AJMartel/BoomBox/fusecontrol.jpg

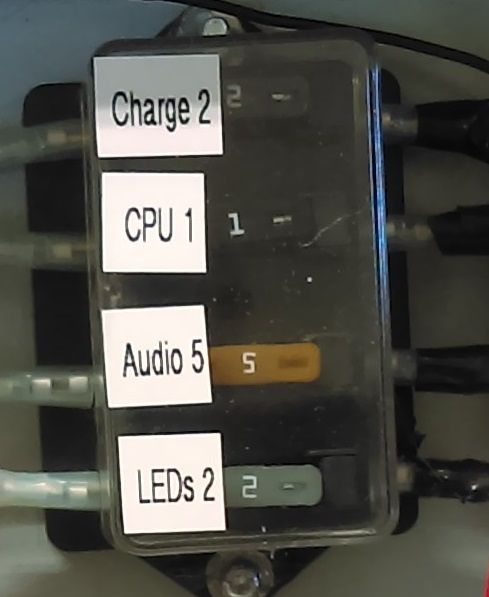
fusecontrol.jpg
