AJMartel/BoomBox/FusePower.jpg

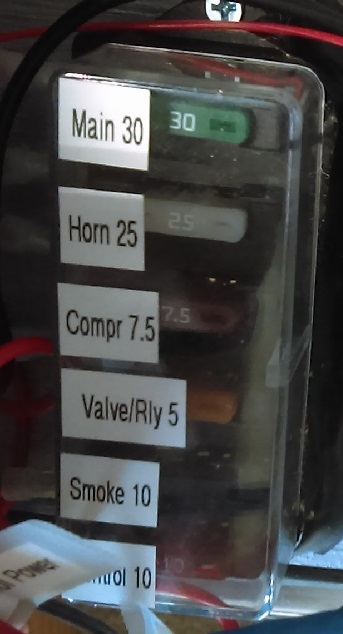
FusePower.jpg
