AJMartel/BoomBox/IMAG0399.jpg

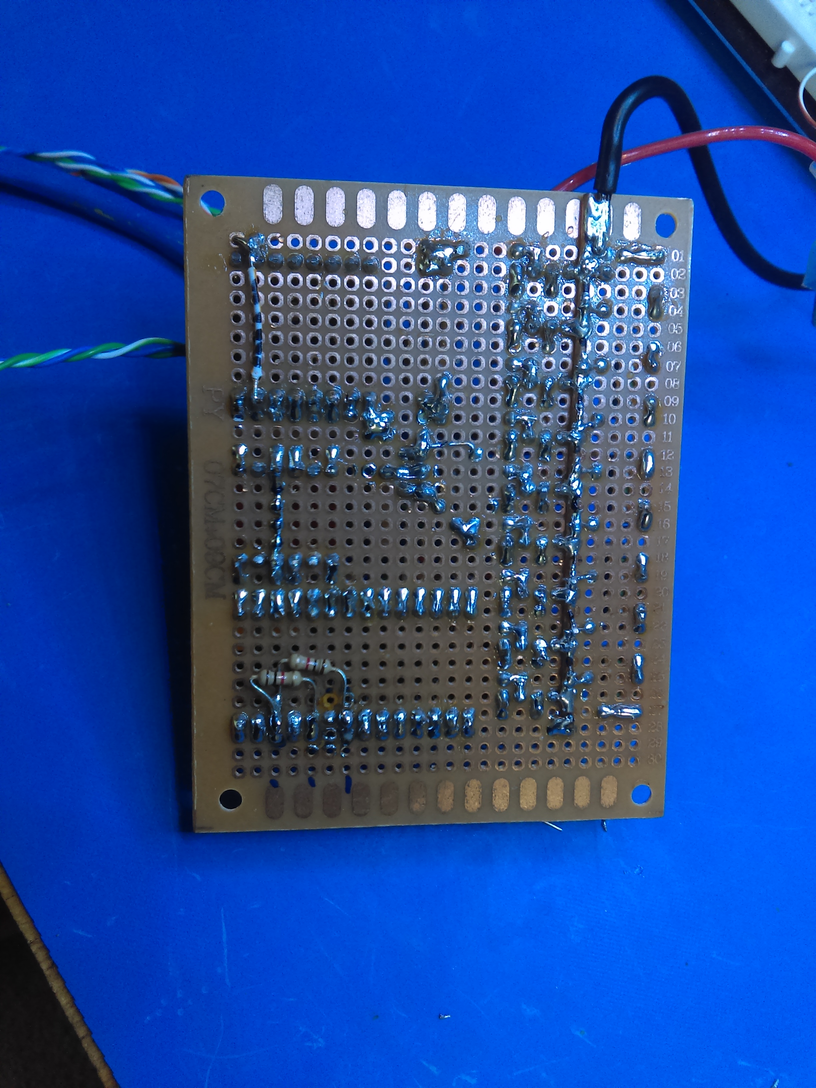
IMAG0399.jpg
