AJMartel/BoomBox/IMAG0400.jpg

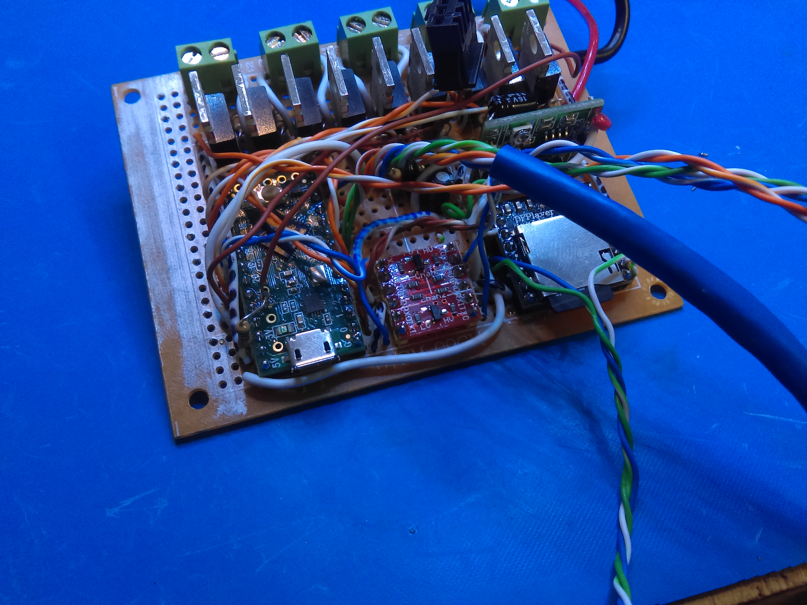
IMAG0400.jpg
