AJMartel/BoomBox/IMAG0402.jpg

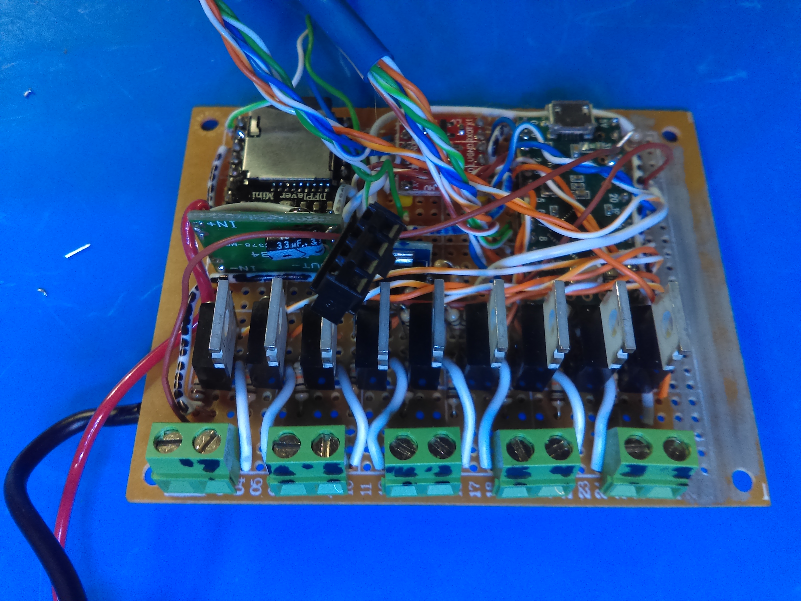
IMAG0402.jpg
