AJMartel/BoomBox/IMAG0403.jpg

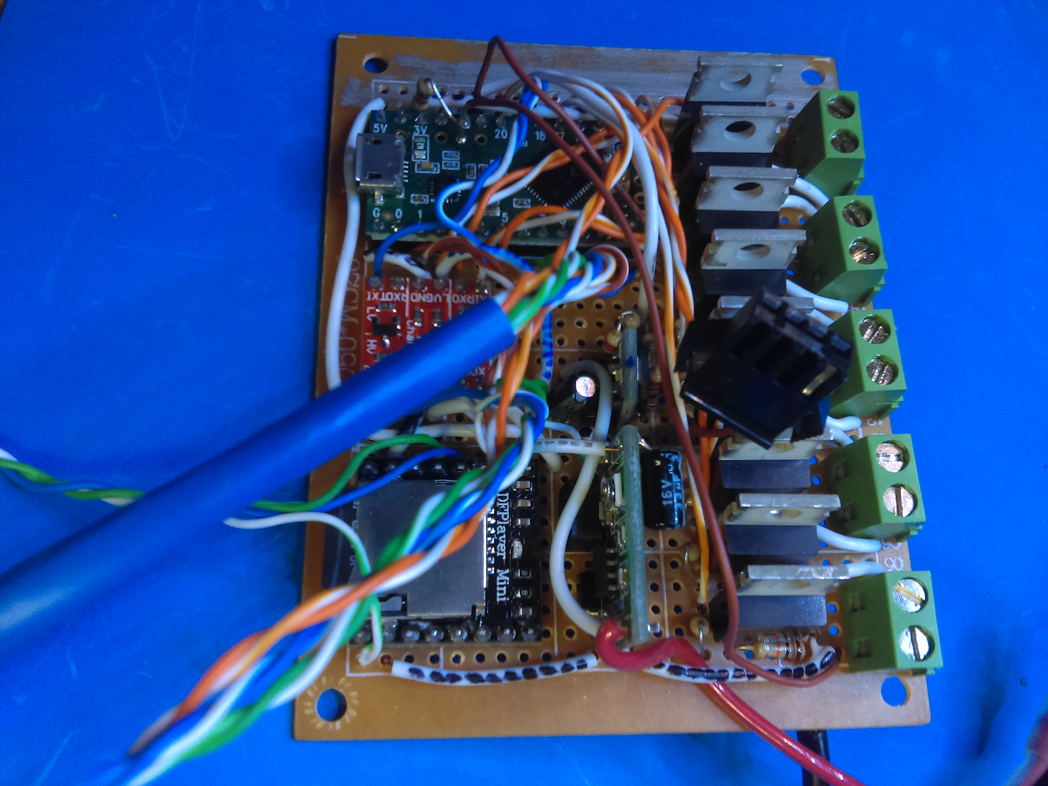
IMAG0403.jpg
