AJMartel/BoomBox/IMAG0406.jpg

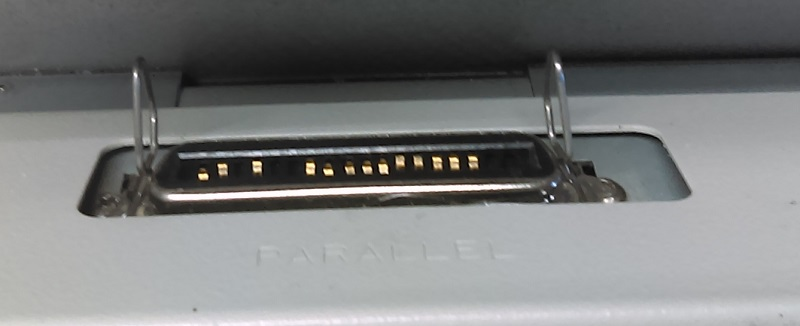
IMAG0406.jpg
