AJMartel/BoomBox/IMAG0410.jpg

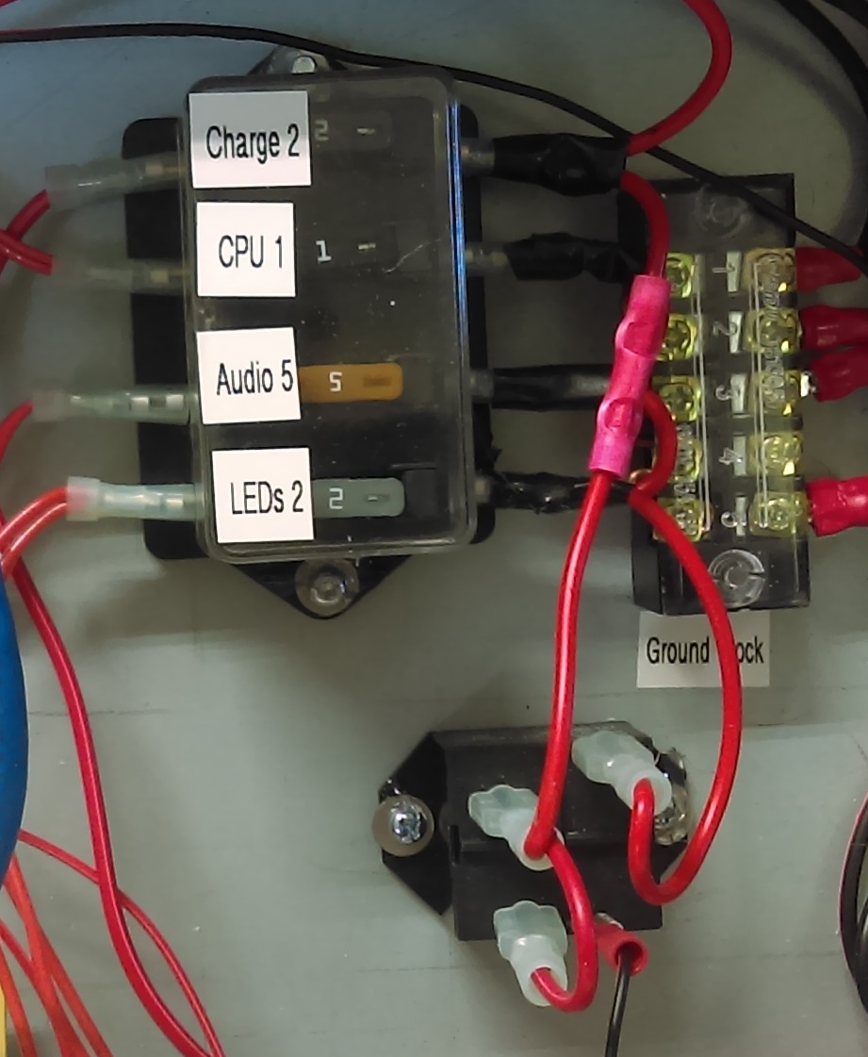
IMAG0410.jpg
