AJMartel/BoomBox/IMAG0411.jpg

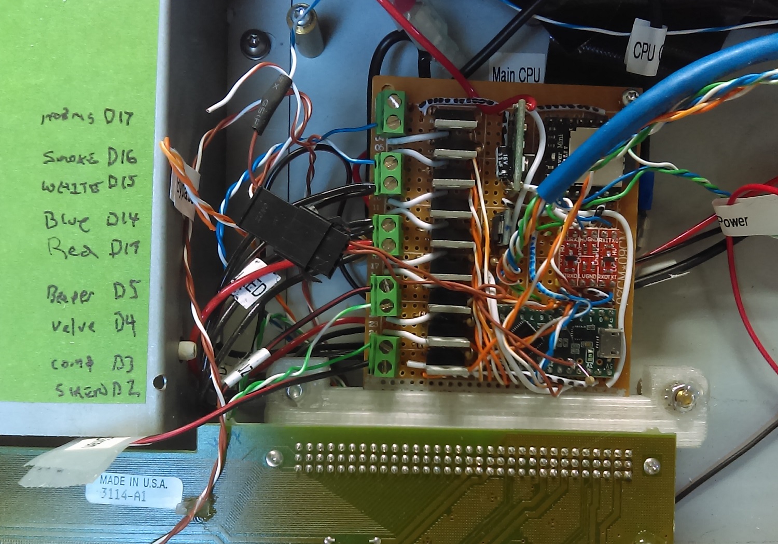
IMAG0411.jpg
