AJMartel/BoomBox/IMAG0413.jpg

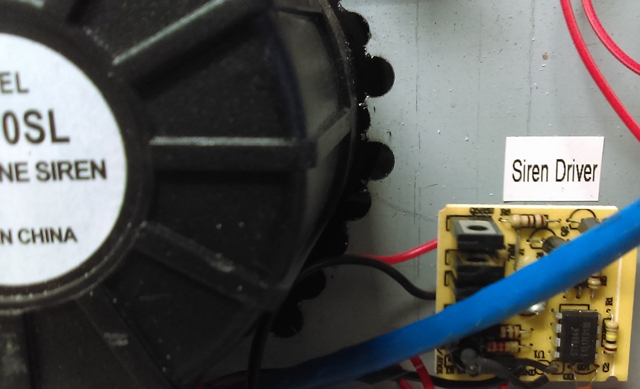
IMAG0413.jpg
