AJMartel/BoomBox/IMAG0414.jpg

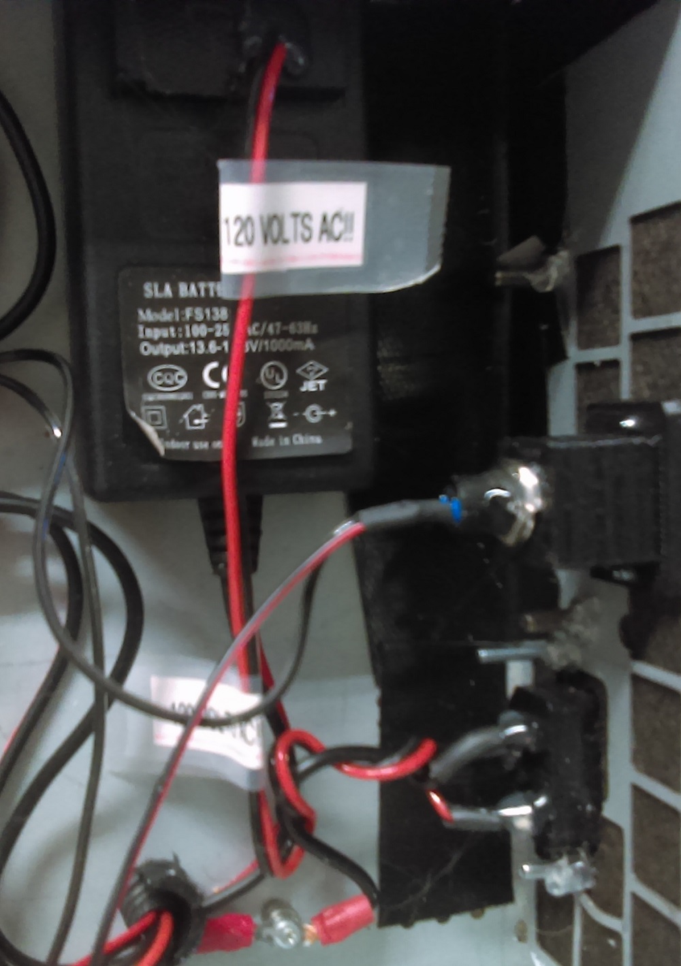
IMAG0414.jpg
