AJMartel/BoomBox/IMAG0417.jpg

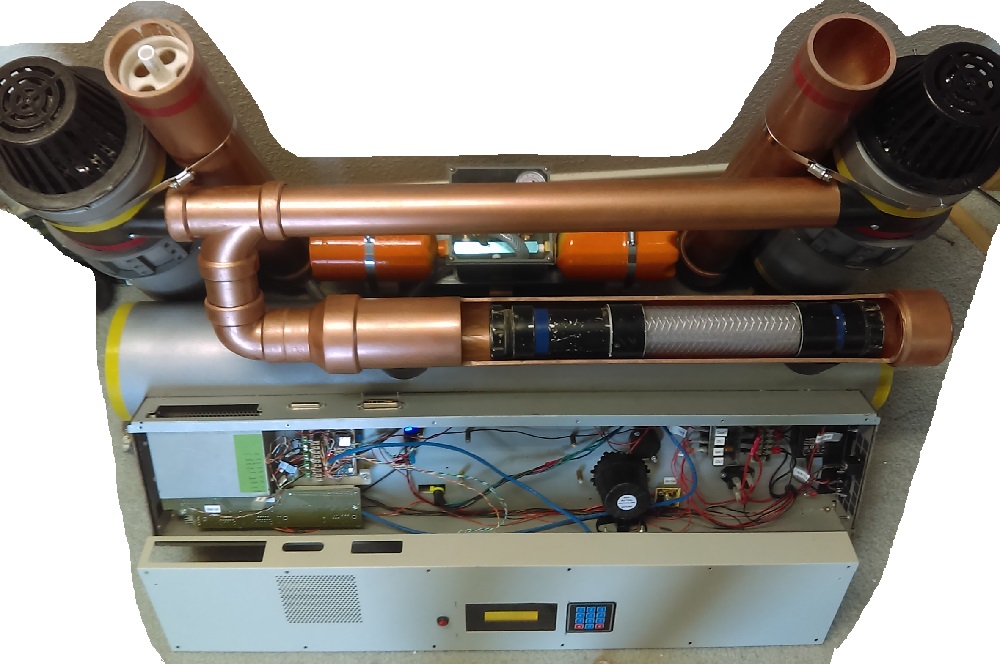
IMAG0417.jpg
