AJMartel/BoomBox/IMAG0419.jpg

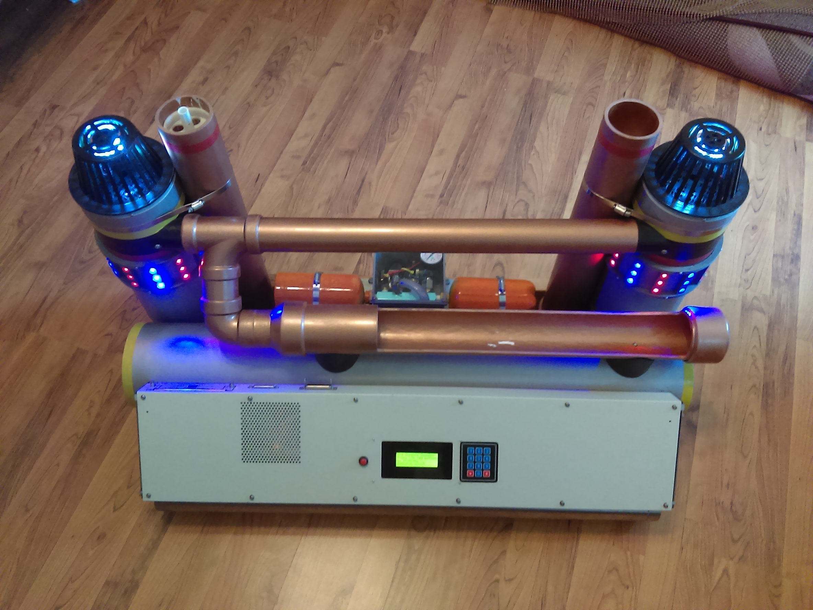
IMAG0419.jpg
