AJMartel/BoomBox/IMAG0420.jpg

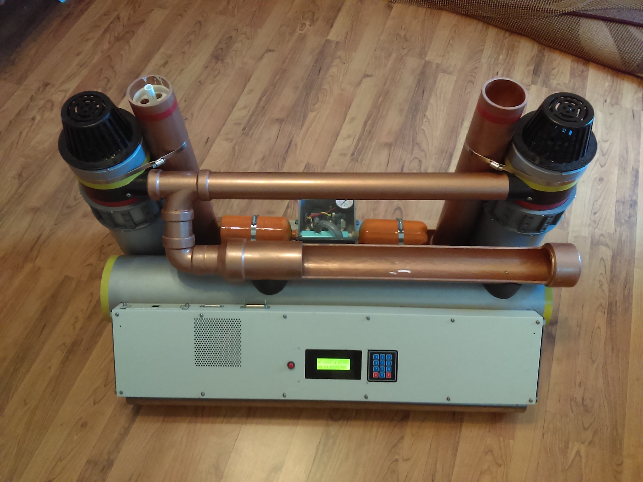
IMAG0420.jpg
