AJMartel/BoomBox/IMAG0421.jpg

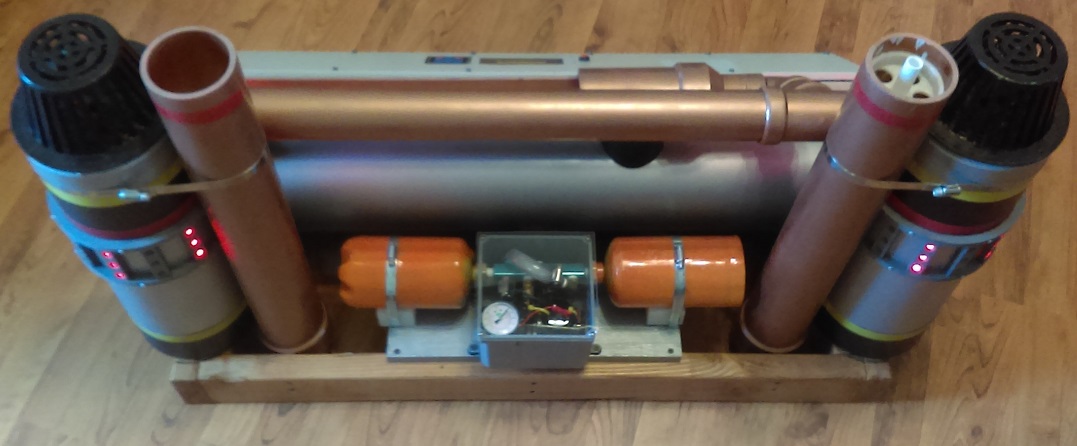
IMAG0421.jpg
