AJMartel/BoomBox/IMAG0423.jpg

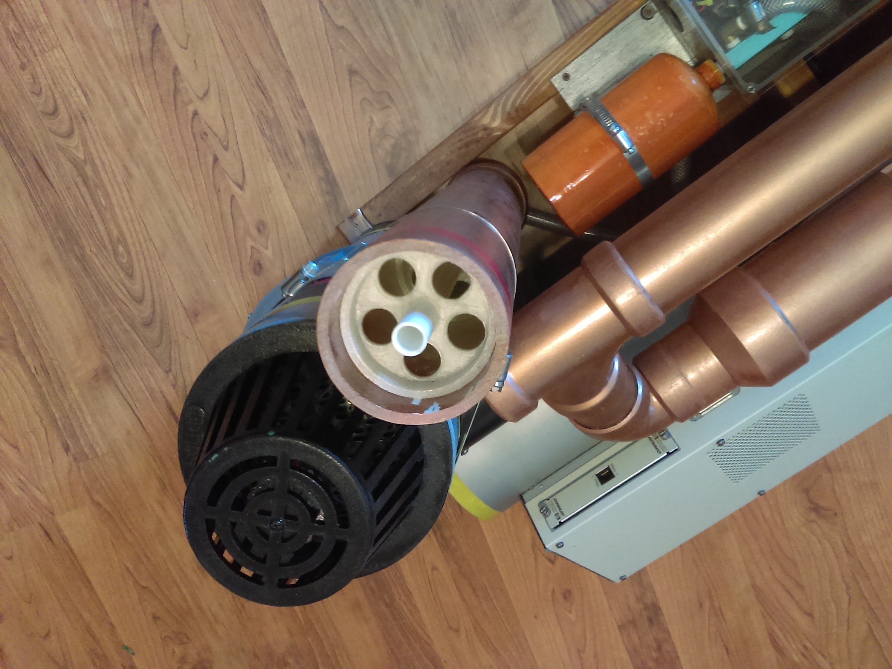
IMAG0423.jpg
