AJMartel/BoomBox/IMAG0424.jpg

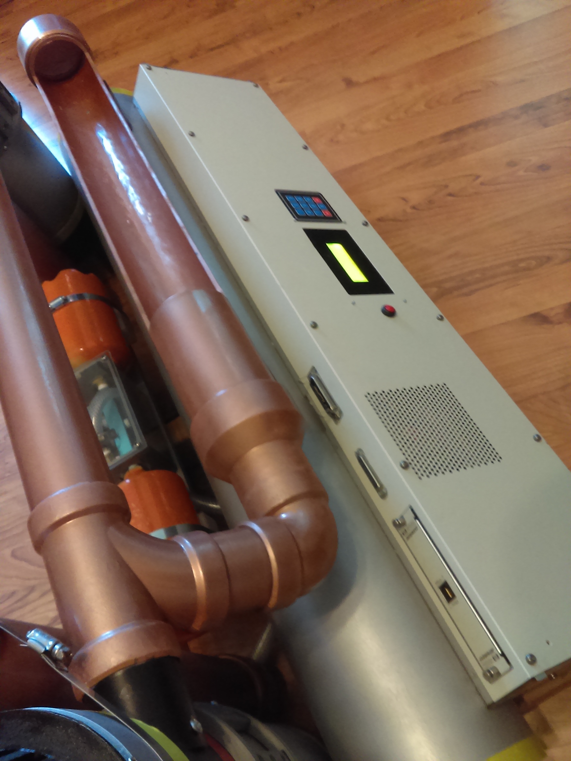
IMAG0424.jpg
