AJMartel/BoomBox/IMAG0426.jpg

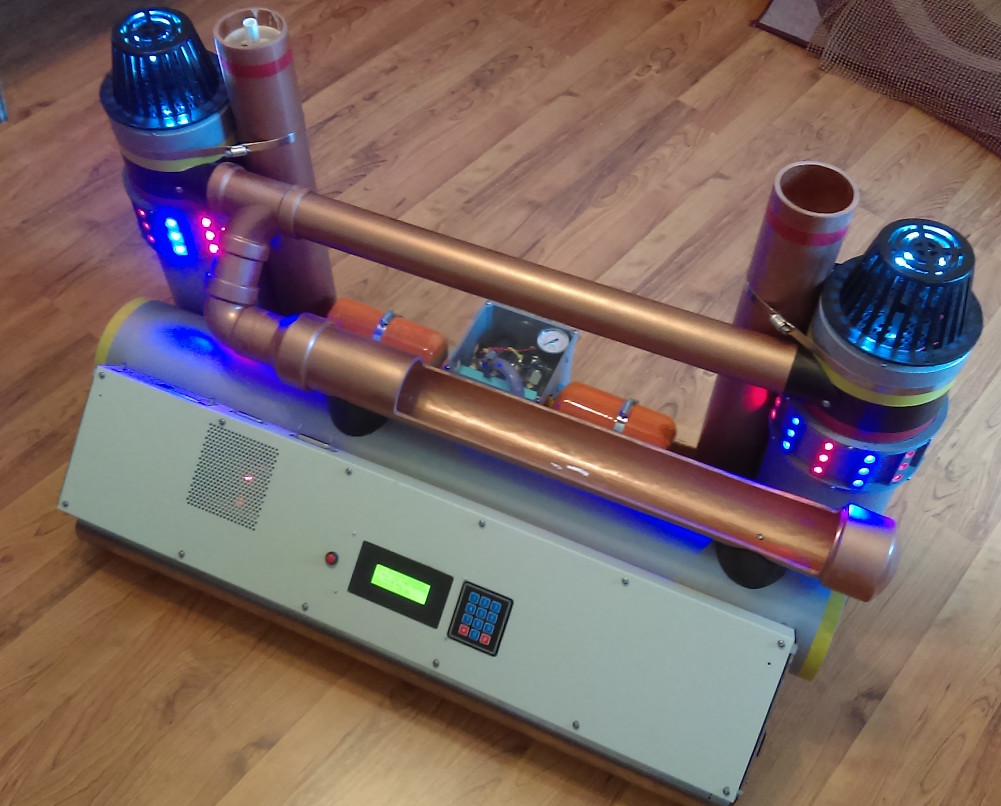
IMAG0426.jpg
