AJMartel/BoomBox/IMAG0428.jpg

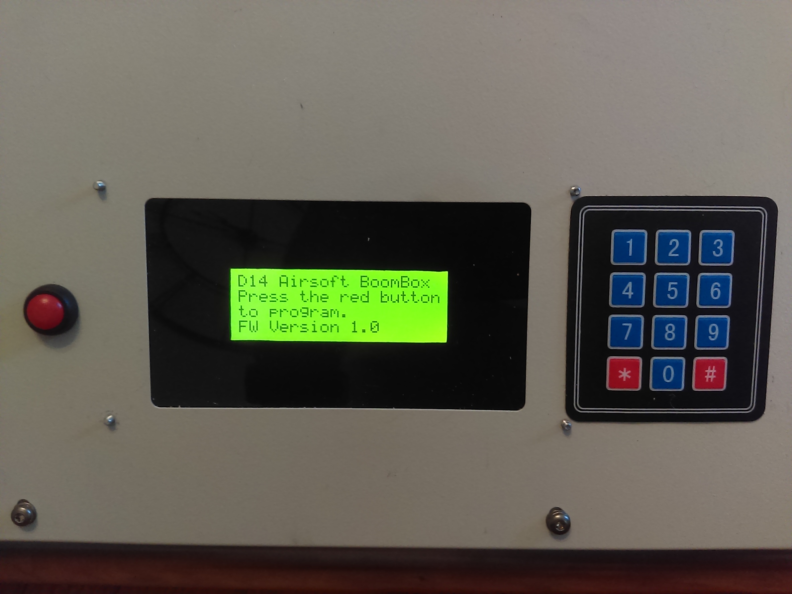
IMAG0428.jpg
