AJMartel/BoomBox/IMAG0429.jpg

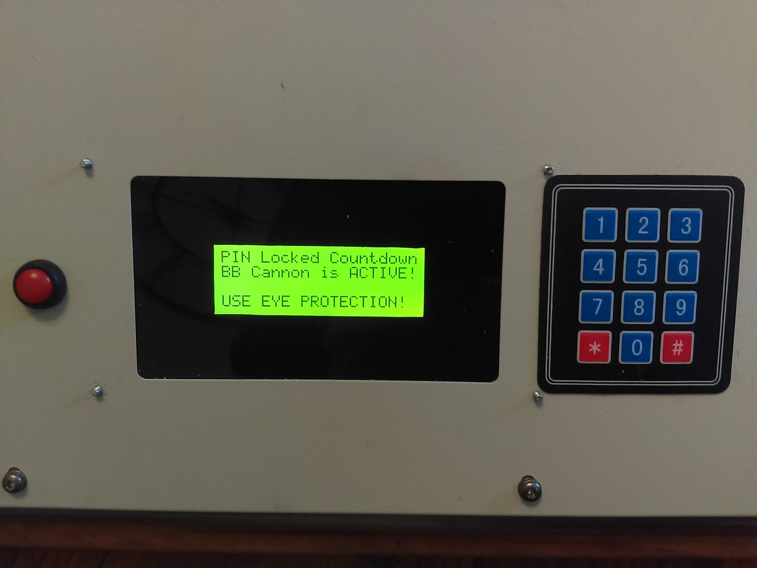
IMAG0429.jpg
