AJMartel/BoomBox/IMAG0430.jpg

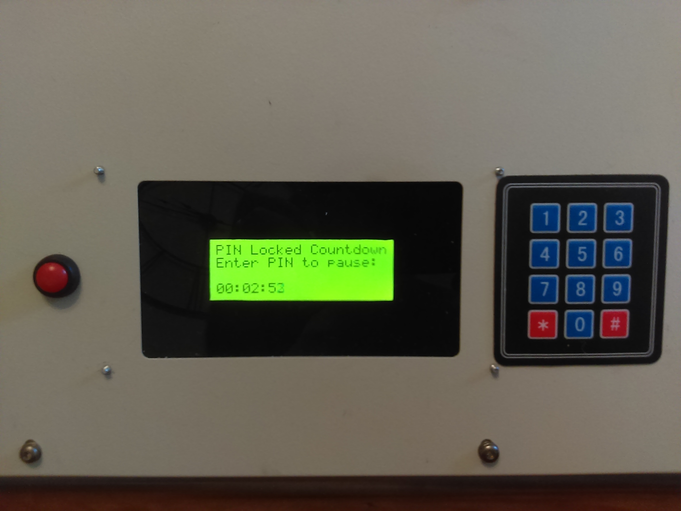
IMAG0430.jpg
