AJMartel/BoomBox/IMAG0433.jpg

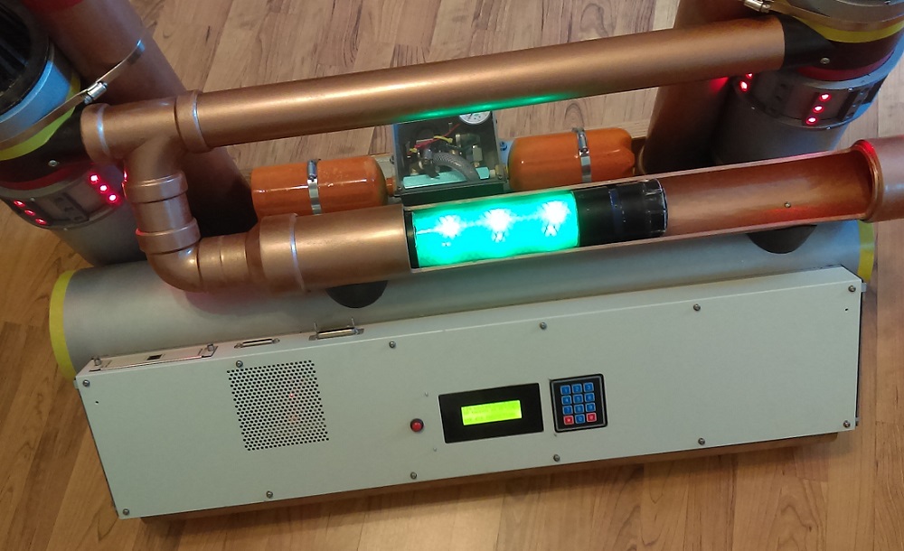
IMAG0433.jpg
